weiliangng/scv2/Core/Src/referee_uart.c

#include "referee_uart.h"

#include <stdbool.h>
#include <stddef.h>

#include "FreeRTOS.h"
#include "task.h"

#include "command_inputs.h"

enum
{
  REF_SOF = 0xA5,
  REF_HDR_LEN = 5,
  REF_CMD_LEN = 2,
  REF_CRC16_LEN = 2,

  REF_CMD_ROBOT_STATUS = 0x0201,
  REF_CMD_POWER_HEAT = 0x0202,
};

enum
{
  REF_0201_CHASSIS_POWER_LIMIT_OFF = 10,
  REF_0202_BUFFER_ENERGY_OFF = 8,
};

typedef enum
{
  REF_PARSE_WAIT_SOF = 0,
  REF_PARSE_HDR = 1,
  REF_PARSE_BODY = 2,
} ref_parse_state_t;

typedef struct
{
  ref_parse_state_t state;
  uint8_t hdr[REF_HDR_LEN];
  uint16_t hdr_idx;
  uint16_t data_len;
  uint16_t body_len;
  uint16_t body_idx;

  uint16_t cmd_id;

  uint16_t crc16_calc;
  uint16_t crc16_rx;

  bool cap_chassis_power_limit_ok;
  uint16_t cap_chassis_power_limit_w;

  bool cap_buffer_energy_ok;
  uint16_t cap_buffer_energy_j;
} referee_parser_t;

static UART_HandleTypeDef *s_huart;
static TaskHandle_t s_parser_task;
static volatile bool s_rx_restart_requested;

static uint8_t s_rx_dma[REFEREE_UART_RX_DMA_SZ];
static uint16_t s_old_pos;
static referee_parser_t s_parser;

static const uint8_t CRC8_INIT = 0xFFU;
static const uint8_t CRC8_TAB[256] = {
    0x00, 0x5e, 0xbc, 0xe2, 0x61, 0x3f, 0xdd, 0x83, 0xc2, 0x9c, 0x7e, 0x20, 0xa3, 0xfd, 0x1f, 0x41,
    0x9d, 0xc3, 0x21, 0x7f, 0xfc, 0xa2, 0x40, 0x1e, 0x5f, 0x01, 0xe3, 0xbd, 0x3e, 0x60, 0x82, 0xdc,
    0x23, 0x7d, 0x9f, 0xc1, 0x42, 0x1c, 0xfe, 0xa0, 0xe1, 0xbf, 0x5d, 0x03, 0x80, 0xde, 0x3c, 0x62,
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
}

static inline uint16_t u16_le(const uint8_t *p)
{
  return (uint16_t)p[0] | (uint16_t)((uint16_t)p[1] << 8U);
}

static void parser_reset(referee_parser_t *p)
{
  *p = (referee_parser_t){
      .state = REF_PARSE_WAIT_SOF,
  };
}

static void parser_accept_frame(referee_parser_t *p)
{
  if (p->cmd_id == REF_CMD_ROBOT_STATUS && p->cap_chassis_power_limit_ok)
  {
    (void)CommandInputs_SetPower(&g_uart_command.power_w,
                                 p->cap_chassis_power_limit_w,
                                 HAL_GetTick());
  }
  else if (p->cmd_id == REF_CMD_POWER_HEAT && p->cap_buffer_energy_ok)
  {
    (void)CommandInputs_SetEnergy(&g_uart_command.energy_j,
                                  p->cap_buffer_energy_j,
                                  HAL_GetTick());
  }
}

static void parser_feed_byte(referee_parser_t *p, uint8_t b)
{
  switch (p->state)
  {
    case REF_PARSE_WAIT_SOF:
      if (b == REF_SOF)
      {
        p->hdr[0] = b;
        p->hdr_idx = 1;
        p->state = REF_PARSE_HDR;
      }
      return;

    case REF_PARSE_HDR:
      p->hdr[p->hdr_idx++] = b;
      if (p->hdr_idx < REF_HDR_LEN)
      {
        return;
      }

      if (crc8_calc(p->hdr, 4U) != p->hdr[4])
      {
        parser_reset(p);
        if (b == REF_SOF)
        {
          p->hdr[0] = b;
          p->hdr_idx = 1;
          p->state = REF_PARSE_HDR;
        }
        return;
      }

      p->data_len = u16_le(&p->hdr[1]);
      if (p->data_len > 256U)
      {
        parser_reset(p);
        return;
      }

      p->body_len = (uint16_t)(REF_CMD_LEN + p->data_len + REF_CRC16_LEN);
      p->body_idx = 0;
      p->cmd_id = 0U;
      p->crc16_calc = CRC16_INIT;
      p->crc16_rx = 0U;
      for (uint32_t i = 0; i < REF_HDR_LEN; i++)
      {
        p->crc16_calc = crc16_update(p->crc16_calc, p->hdr[i]);
      }

      p->cap_chassis_power_limit_ok = false;
      p->cap_buffer_energy_ok = false;
      p->state = REF_PARSE_BODY;
      return;

    case REF_PARSE_BODY:
      if (p->body_idx < (uint16_t)(p->body_len - REF_CRC16_LEN))
      {
        p->crc16_calc = crc16_update(p->crc16_calc, b);
      }

      if (p->body_idx == 0)
      {
        p->cmd_id = (uint16_t)b;
      }
      else if (p->body_idx == 1)
      {
        p->cmd_id |= (uint16_t)((uint16_t)b << 8U);
      }
      else if (p->body_idx == (uint16_t)(p->body_len - 2U))
      {
        p->crc16_rx = (uint16_t)b;
      }
      else if (p->body_idx == (uint16_t)(p->body_len - 1U))
      {
        p->crc16_rx |= (uint16_t)((uint16_t)b << 8U);
      }
      else
      {
        const uint16_t payload_idx = (uint16_t)(p->body_idx - REF_CMD_LEN);
        if (p->cmd_id == REF_CMD_ROBOT_STATUS &&
            payload_idx == REF_0201_CHASSIS_POWER_LIMIT_OFF &&
            p->data_len >= (uint16_t)(REF_0201_CHASSIS_POWER_LIMIT_OFF + 2U))
        {
          p->cap_chassis_power_limit_w = (uint16_t)b;
        }
        else if (p->cmd_id == REF_CMD_ROBOT_STATUS &&
                 payload_idx == (uint16_t)(REF_0201_CHASSIS_POWER_LIMIT_OFF + 1U) &&
                 p->data_len >= (uint16_t)(REF_0201_CHASSIS_POWER_LIMIT_OFF + 2U))
        {
          p->cap_chassis_power_limit_w |= (uint16_t)((uint16_t)b << 8U);
          p->cap_chassis_power_limit_ok = true;
        }
        else if (p->cmd_id == REF_CMD_POWER_HEAT &&
                 payload_idx == REF_0202_BUFFER_ENERGY_OFF &&
                 p->data_len >= (uint16_t)(REF_0202_BUFFER_ENERGY_OFF + 2U))
        {
          p->cap_buffer_energy_j = (uint16_t)b;
        }
        else if (p->cmd_id == REF_CMD_POWER_HEAT &&
                 payload_idx == (uint16_t)(REF_0202_BUFFER_ENERGY_OFF + 1U) &&
                 p->data_len >= (uint16_t)(REF_0202_BUFFER_ENERGY_OFF + 2U))
        {
          p->cap_buffer_energy_j |= (uint16_t)((uint16_t)b << 8U);
          p->cap_buffer_energy_ok = true;
        }
      }

      p->body_idx++;
      if (p->body_idx < p->body_len)
      {
        return;
      }

      if (p->crc16_calc == p->crc16_rx)
      {
        parser_accept_frame(p);
      }

      parser_reset(p);
      return;
  }
}

static void parser_feed(referee_parser_t *p, const uint8_t *buf, uint32_t len)
{
  for (uint32_t i = 0; i < len; i++)
  {
    parser_feed_byte(p, buf[i]);
  }
}

static void notify_parser_from_isr(void)
{
  if (s_parser_task == NULL)
  {
    return;
  }

  BaseType_t hpw = pdFALSE;
  vTaskNotifyGiveFromISR(s_parser_task, &hpw);
  portYIELD_FROM_ISR(hpw);
}

void RefereeUart_UsartIdleIsr(UART_HandleTypeDef *huart)
{
  if (s_huart == NULL || huart != s_huart)
  {
    return;
  }
  if (__HAL_UART_GET_FLAG(huart, UART_FLAG_IDLE) == RESET)
  {
    return;
  }
  if (__HAL_UART_GET_IT_SOURCE(huart, UART_IT_IDLE) == RESET)
  {
    return;
  }

  __HAL_UART_CLEAR_IDLEFLAG(huart);
  notify_parser_from_isr();
}

void HAL_UART_RxHalfCpltCallback(UART_HandleTypeDef *huart)
{
  if (s_huart == NULL || huart != s_huart)
  {
    return;
  }
  notify_parser_from_isr();
}

void HAL_UART_RxCpltCallback(UART_HandleTypeDef *huart)
{
  if (s_huart == NULL || huart != s_huart)
  {
    return;
  }
  notify_parser_from_isr();
}

void HAL_UART_ErrorCallback(UART_HandleTypeDef *huart)
{
  if (s_huart == NULL || huart != s_huart)
  {
    return;
  }
  s_rx_restart_requested = true;
  notify_parser_from_isr();
}

static uint16_t dma_pos(const UART_HandleTypeDef *huart)
{
  const uint16_t ndtr1 = (uint16_t)__HAL_DMA_GET_COUNTER(huart->hdmarx);
  const uint16_t ndtr2 = (uint16_t)__HAL_DMA_GET_COUNTER(huart->hdmarx);
  const uint16_t ndtr = (ndtr2 == ndtr1) ? ndtr1 : ndtr2;
  if (ndtr > (uint16_t)REFEREE_UART_RX_DMA_SZ)
  {
    return 0U;
  }
  return (uint16_t)((uint16_t)REFEREE_UART_RX_DMA_SZ - ndtr);
}

void RefereeUart_Task(UART_HandleTypeDef *huart)
{
  s_huart = huart;
  s_parser_task = xTaskGetCurrentTaskHandle();
  s_old_pos = 0U;
  parser_reset(&s_parser);

  (void)HAL_UART_Receive_DMA(huart, s_rx_dma, (uint16_t)REFEREE_UART_RX_DMA_SZ);
  __HAL_DMA_ENABLE_IT(huart->hdmarx, DMA_IT_HT);
  __HAL_UART_CLEAR_IDLEFLAG(huart);
  __HAL_UART_ENABLE_IT(huart, UART_IT_IDLE);

  for (;;)
  {
    (void)ulTaskNotifyTake(pdTRUE, portMAX_DELAY);

    if (s_rx_restart_requested)
    {
      s_rx_restart_requested = false;
      (void)HAL_UART_AbortReceive(huart);
      (void)HAL_UART_Receive_DMA(huart, s_rx_dma, (uint16_t)REFEREE_UART_RX_DMA_SZ);
      __HAL_DMA_ENABLE_IT(huart->hdmarx, DMA_IT_HT);
      __HAL_UART_CLEAR_IDLEFLAG(huart);
      __HAL_UART_ENABLE_IT(huart, UART_IT_IDLE);
      s_old_pos = dma_pos(huart);
      parser_reset(&s_parser);
    }

    const uint16_t pos = dma_pos(huart);
    if (pos == s_old_pos)
    {
      continue;
    }

    if (pos > s_old_pos)
    {
      parser_feed(&s_parser, &s_rx_dma[s_old_pos], (uint32_t)(pos - s_old_pos));
    }
    else
    {
      parser_feed(&s_parser, &s_rx_dma[s_old_pos], (uint32_t)(REFEREE_UART_RX_DMA_SZ - s_old_pos));
      if (pos > 0U)
      {
        parser_feed(&s_parser, &s_rx_dma[0], (uint32_t)pos);
      }
    }
    s_old_pos = pos;
  }
}
